erwandavydoff-spec/main-robotique-ia/assets/3Dparts.jpg

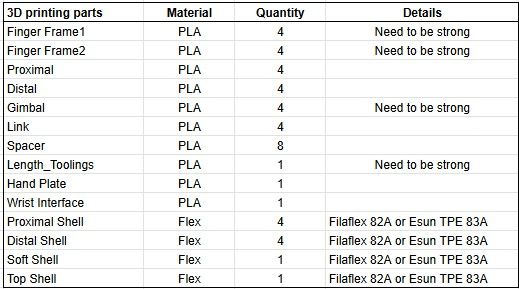
assets/3Dparts.jpg
