erwandavydoff-spec/main-robotique-ia/assets/3DPrint.jpg

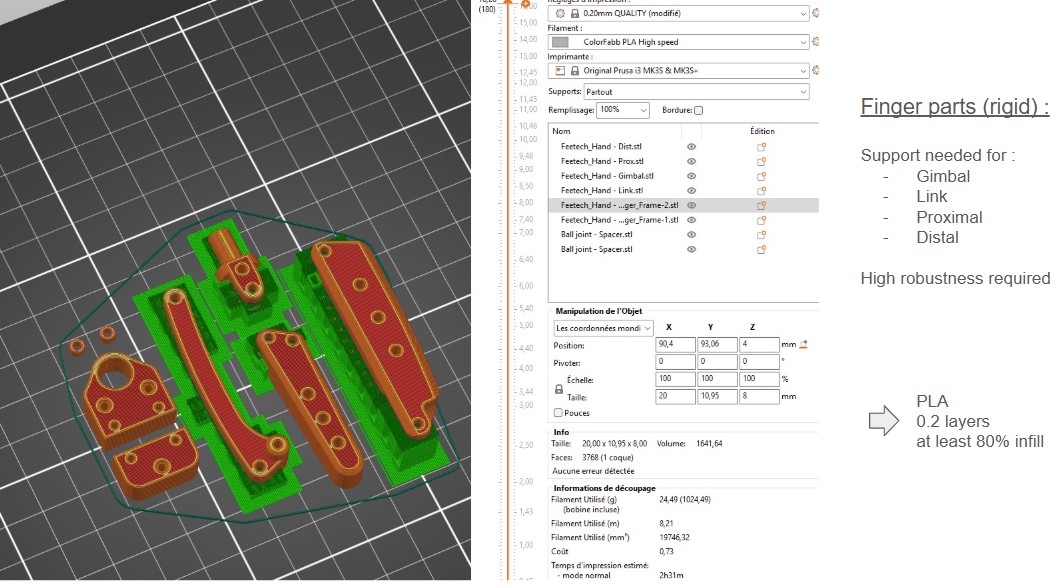
assets/3DPrint.jpg
