erwandavydoff-spec/main-robotique-ia/assets/AmazingHand_Couv.jpg

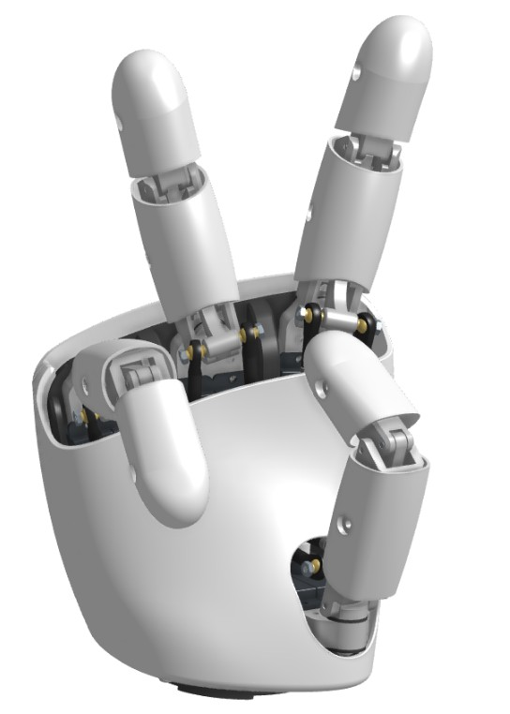
assets/AmazingHand_Couv.jpg
