erwandavydoff-spec/main-robotique-ia/assets/AmazingHandControl.jpg

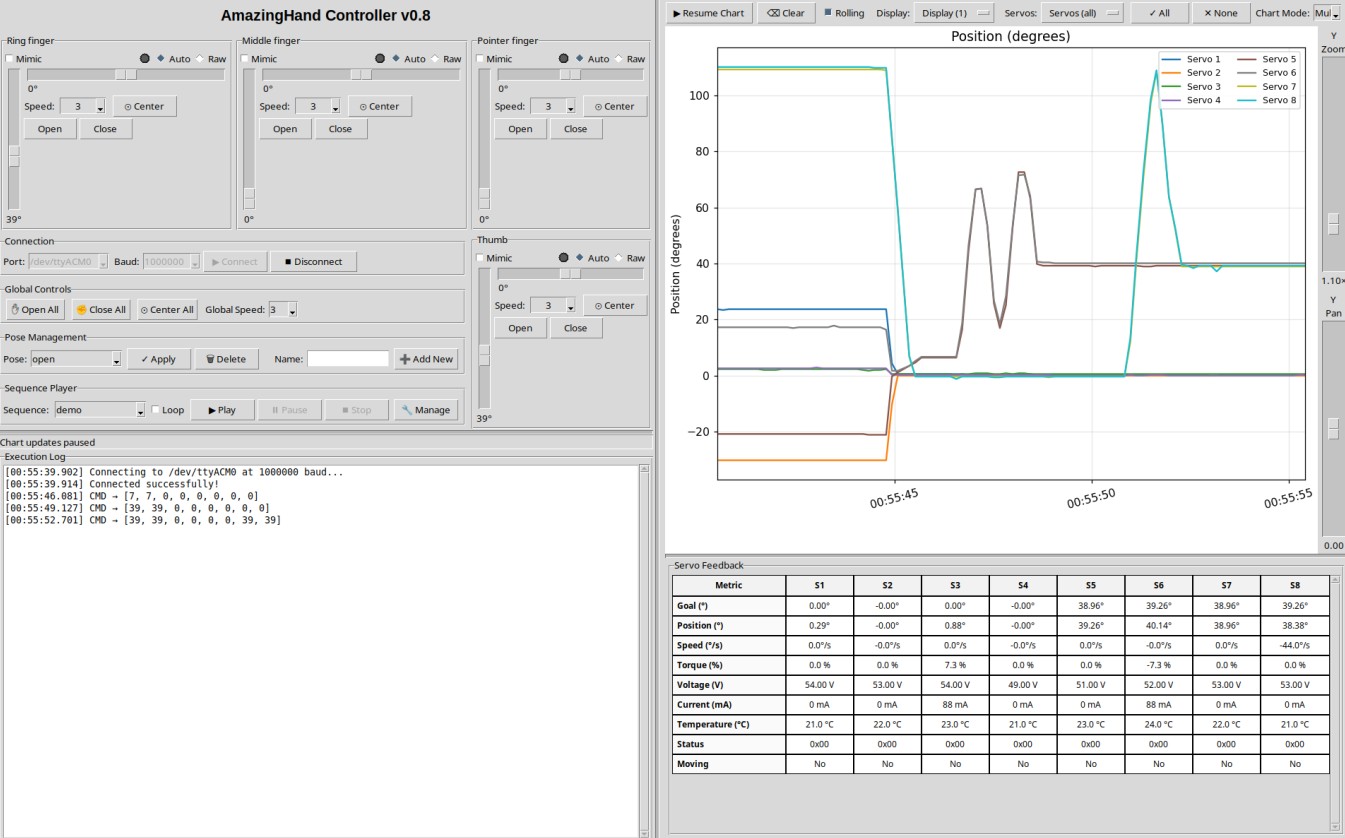
assets/AmazingHandControl.jpg
