erwandavydoff-spec/main-robotique-ia/assets/Arduino_Control-mode.jpg

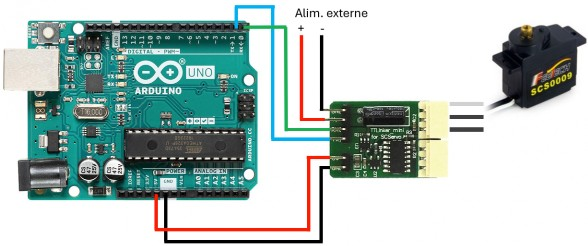
assets/Arduino_Control-mode.jpg
