erwandavydoff-spec/main-robotique-ia/assets/Arduino_Link-mode.jpg

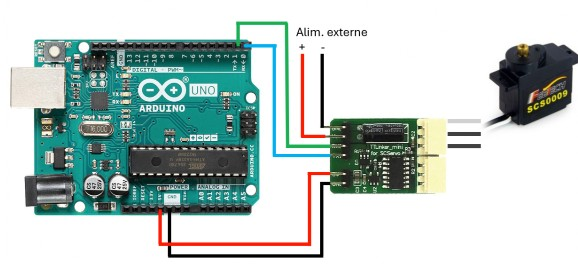
assets/Arduino_Link-mode.jpg
