erwandavydoff-spec/main-robotique-ia/assets/Arduino_Mega.jpg

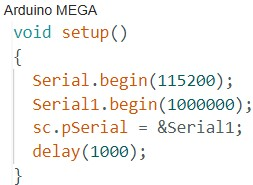
assets/Arduino_Mega.jpg
