erwandavydoff-spec/main-robotique-ia/assets/Base.jpg

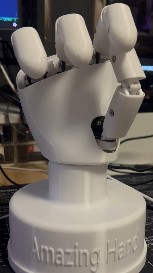
assets/Base.jpg
