erwandavydoff-spec/main-robotique-ia/assets/basic_demo_shot.png

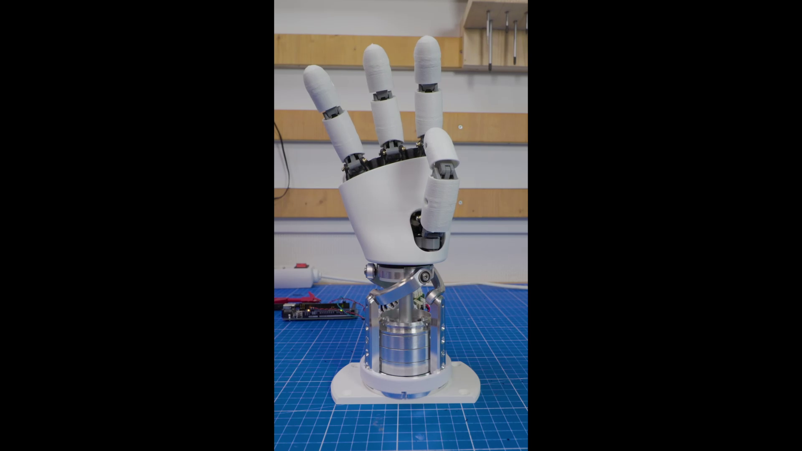
assets/basic_demo_shot.png
