erwandavydoff-spec/main-robotique-ia/assets/Both_Hands-IDs.jpg

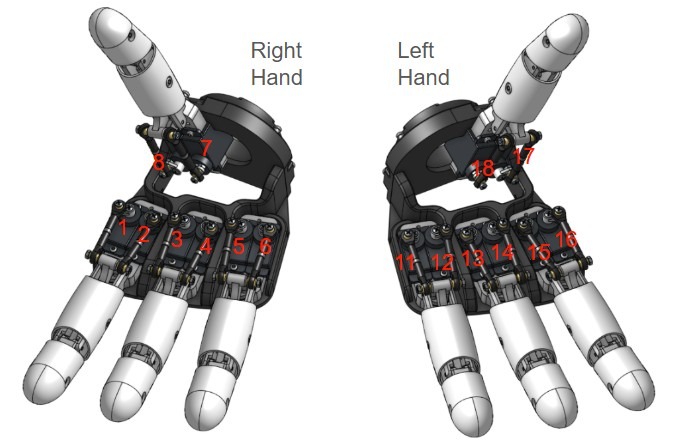
assets/Both_Hands-IDs.jpg
