erwandavydoff-spec/main-robotique-ia/assets/FD_IDs.jpg

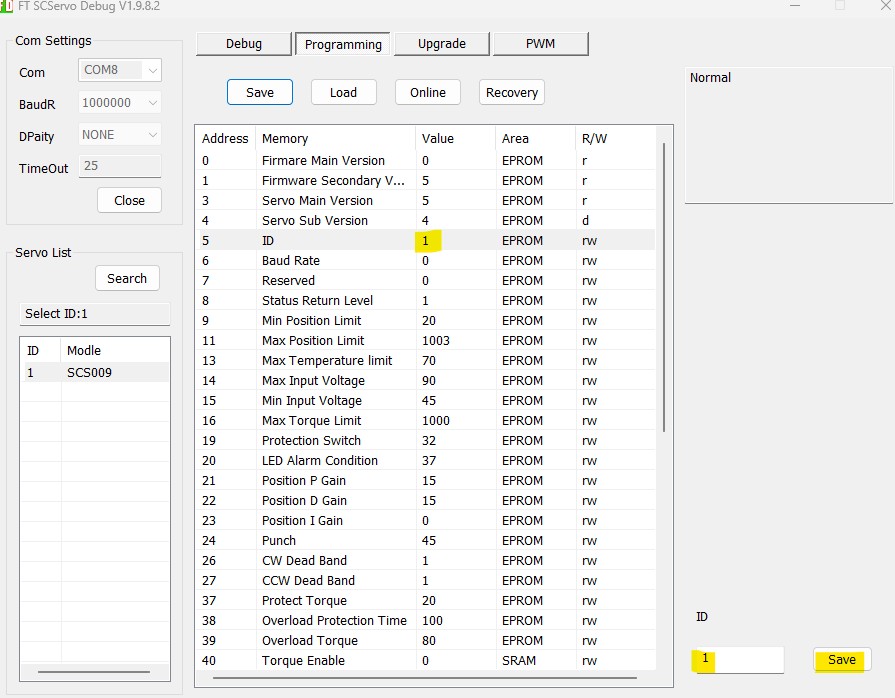
assets/FD_IDs.jpg
