erwandavydoff-spec/main-robotique-ia/assets/Force_control.jpg

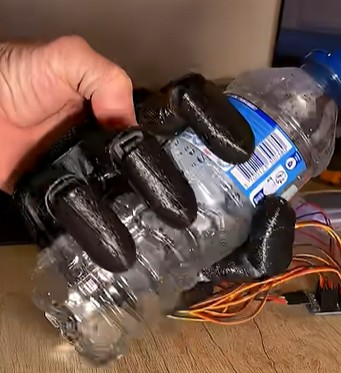
assets/Force_control.jpg
