erwandavydoff-spec/main-robotique-ia/assets/hand_tracking.png

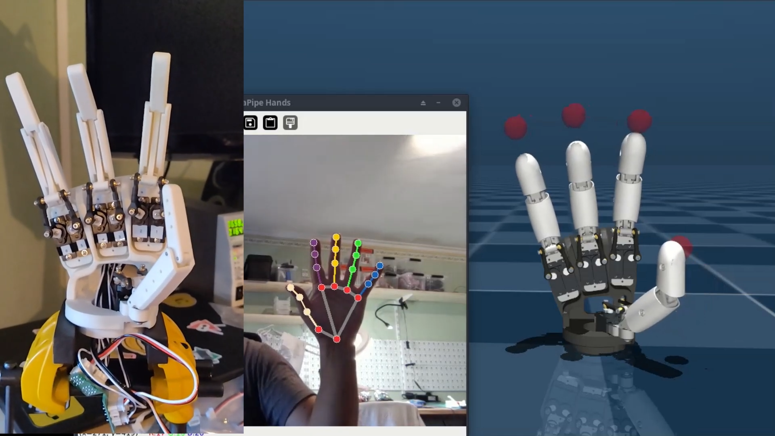
assets/hand_tracking.png
