erwandavydoff-spec/main-robotique-ia/assets/Heart.jpg

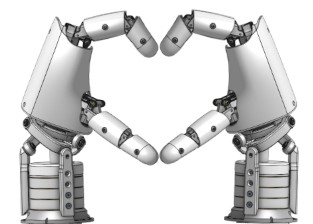
assets/Heart.jpg
