erwandavydoff-spec/main-robotique-ia/assets/Named_Pos.jpg

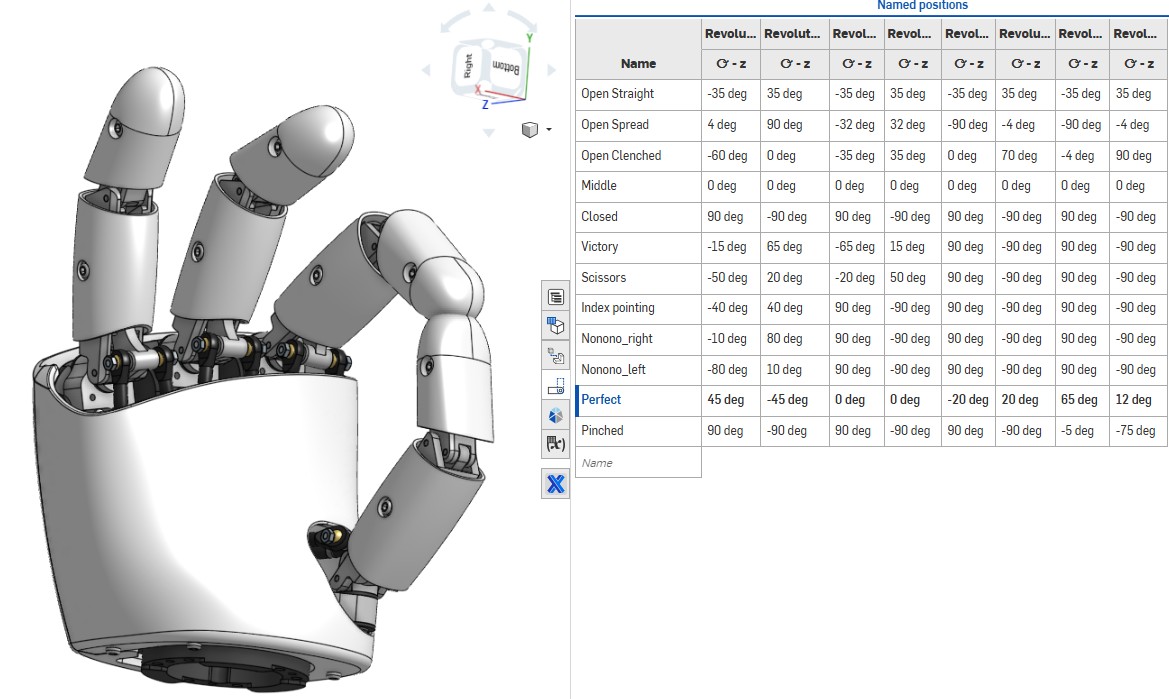
assets/Named_Pos.jpg
