erwandavydoff-spec/main-robotique-ia/assets/Reachy.jpg

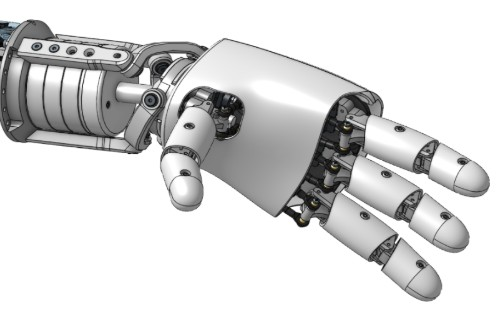
assets/Reachy.jpg
