erwandavydoff-spec/main-robotique-ia/assets/SoHand.jpg

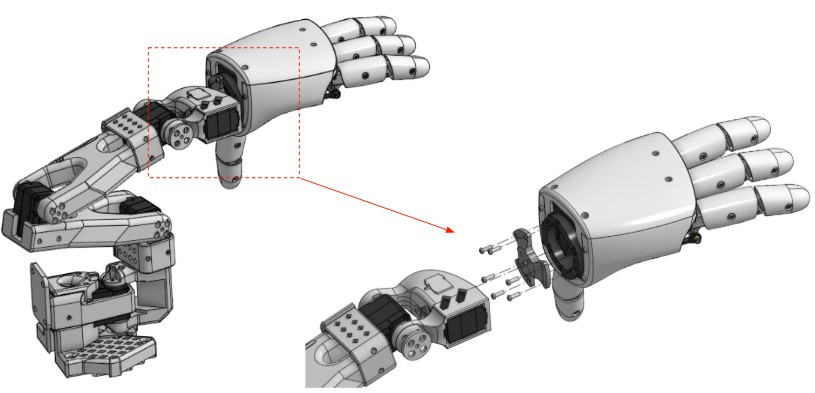
assets/SoHand.jpg
