erwandavydoff-spec/main-robotique-ia/assets/BOM.jpg

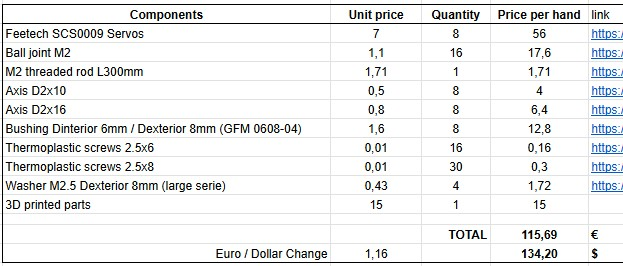
assets/BOM.jpg
