erwandavydoff-spec/main-robotique-ia/assets/Force_control_setup.jpg

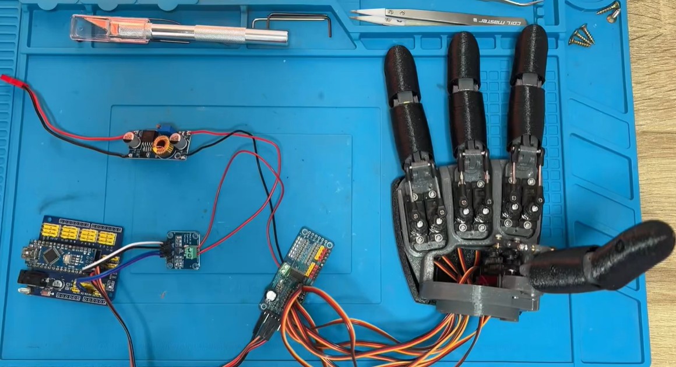
assets/Force_control_setup.jpg
